JakubBohunicky/Oscilloscope/Sim/opamps.cir

[Main]
FileType=CIR
Version=12.00
Program=Micro-Cap
Component Version=10.00
Shape Version=11.00
Screen=2560,1440
MCAPVersion=12.2.0.5
Key ID=Demo
NLCnt=83
TXCnt=0

[shapedef]
Name=Battery
Line=0,0,22,0
Line=22,-3,22,3
Line=26,-7,26,7
Line=26,0,48,0
Current=32,8,16,8

[shapedef]
Name=Ground
Line=0,0,12,0
Line=12,-8,12,8
Line=18,-4,18,4
Line=24,0,24,0

[shapedef]
Name=Minus.root
Line=-2,0,2,0

[shapedef]
Name=Opamp7e
Root="Plus.root",14,6,0
Root="Minus.root",14,42,0
Line=0,0,8,0
Line=0,48,8,48
Line=8,-8,8,56
Line=8,56,72,24
Line=8,-8,72,24
Line=88,16,62,16
Line=56,32,88,32
Line=24,48,24,64
Line=24,0,24,-16
Root="Plus.root",18,-14,0
Root="Minus.root",18,62,0
Line=8,24,0,24
Ellipse=58,14,62,18
FColor=None

[shapedef]
Name=Plus.root
Line=-2,0,2,0
Line=0,-2,0,2

[shapedef]
Name=Resistor
PolyOpen=12
PolyLine=0,0
PolyLine=0,0
PolyLine=12,0
PolyLine=14,-4
PolyLine=18,4
PolyLine=22,-4
PolyLine=26,4
PolyLine=30,-4
PolyLine=34,4
PolyLine=36,0
PolyLine=48,0
PolyLine=48,0
Current=32,8,16,8

[shapedef]
Name=Sine_Source
Root="Vsource.root",0,0,0
Line=24,-6,26,-4
Line=26,-4,26,-2
Line=26,-2,22,2
Line=22,2,22,4
Line=22,4,24,6

[shapedef]
Name=Vsource.root
Line=0,0,12,0
Line=36,0,48,0
Ellipse=12,-12,36,12
FColor=None
Line=7,5,7,9
Root="Plus.root",41,7,0
Current=32,16,16,16

[compdef]
Name=Battery
Definition=Battery
Shape=Battery
Mask=6913
Used=55
memo=Battery
Label Offset=19,7,10,13
PinCnt=2
Pin="Plus",6,0,-4,-5
Pin="Minus",0,0,-10,-5

[compdef]
Name=Ground
Definition=Ground
Shape=Ground
Mask=1793
Used=308
memo=Ground
Label Offset=0,0,0,0
PinCnt=1
Pin="PinA",0,0,-3,-7

[compdef]
Name=Sine Source
Definition=Sine source
Shape=Sine_Source
Mask=4864
Used=1
memo=Sine Source
Label Offset=18,12,15,12
PinCnt=2
Pin="Plus",6,0,-6,-6
Pin="Minus",0,0,-19,-6

[compdef]
Name=Resistor
Definition=Resistor
Shape=Resistor
Mask=7937
Used=205
memo=Resistor
Label Offset=18,6,8,11
PinCnt=2
Pin="Plus",6,0,-10,-4
Pin="Minus",0,0,-14,-4

[compdef]
Name=AD8138_AD
Definition=Subckt
Shape=Opamp7e
Mask=4224
memo=Low Distortion Differential ADC Driver
Label Offset=46,40,-5,39
PinCnt=7
Pin="3A",a,0,0,-9,0
Pin="9",a,0,6,-3,0
Pin="99",a,3,-2,5,8
Pin="98",a,3,8,4,7
Pin="71",a,11,2,-5,0
Pin="71B",a,11,4,-5,0
Pin="110",a,0,3,-13,0

[compdef]
Name=ISL55211
Definition=Subckt
Shape=Opamp7e
Mask=4224
memo=Wideband, Low Noise, Low Distortion, Fixed Gain, Differential Amplifier BW=1.4GHz SR=5600V/us Av=2
Link=http://www.intersil.com/data/fn/fn7868.pdf
Label Offset=54,35,-4,43
PinCnt=7
Pin="IN-",a,0,6,-10,0
Pin="IN+",a,0,0,-10,0
Pin="V-",a,3,8,6,9
Pin="OUT-",a,11,2
Pin="OUT+",a,11,4
Pin="VCM",a,0,3,-18,0
Pin="V+",a,3,-2,5,6

[Circuit]
Window Placement=2,3, -1,-1, -8,-31, 0,0,1460,489
Default Object=Color=#000080
Default Object Font=Height=-15,FStyle=0,Color=#000080,Name=Arial
Default Object Apply Border To Text=No
Default Object Apply Fill To Text=No
Default Object GridSnap=No
NodeVoltageFormat=3
CurrentFormat=3
PowerFormat=3
PathDelayFormat=3
WarningFormat=3
GridTextFormulaFormat=3
Window Placement in Transient Probe=0,1, -1,-1, -8,-30, 633,0,1266,760
SpiceType=AMBIGUOUS
Title_Block_Border=None
Title_Block=False
Show Nodes=False
Show Voltages=True
Show Current=False
Show Power=False
Show Condition=False
Show Pin Connections=False
Show Connection Warnings=False
Show Cross=False
Show Attribute Text=True
Show Grid Text=True

[Comp]
Name=Battery
Px=168,312
Rot=3

[Attr]
ON=-26,-27,PART
V=V1
Style=8192

[Attr]
ON=-18,-41,VALUE
V=5
Style=8192

[Attr]
ON=0,0,PACKAGE
V

[Comp]
Name=Battery
Px=160,448
Rot=3

[Attr]
ON=-26,-27,PART
V=V2
Style=8192

[Attr]
ON=-18,-41,VALUE
V=5
Style=8192

[Attr]
ON=0,0,PACKAGE
V

[Wire]
Pxs=168,264,400,264

[Wire]
Pxs=400,264,400,304

[Wire]
Pxs=168,312,168,360

[Wire]
Pxs=160,400,168,400

[Comp]
Name=Ground
Px=168,360

[Wire]
Pxs=168,360,168,400

[Comp]
Name=Ground
Px=224,16
Rot=1

[Wire]
Pxs=160,448,400,448

[Wire]
Pxs=400,384,400,448

[Comp]
Name=Ground
Px=272,384
Rot=1

[Comp]
Name=Sine Source
Px=272,384
Rot=3

[Attr]
ON=-31,-26,PART
V=V3
Style=8192

[Attr]
ON=-39,-40,MODEL
V=fdfd

[Attr]
ON=0,0,PACKAGE
V

[Comp]
Name=Resistor
Px=320,328
Rot=4

[Attr]
ON=18,-20,PART
V=R1
Style=8192

[Attr]
ON=18,-34,RESISTANCE
V=500
Style=8192

[Attr]
ON=0,0,PACKAGE
V

[Comp]
Name=Resistor
Px=320,376
Rot=4

[Attr]
ON=-7,-18,PART
V=R2
Style=8192

[Attr]
ON=18,-33,RESISTANCE
V=523
Style=8192

[Attr]
ON=0,0,PACKAGE
V

[Wire]
Pxs=272,328,320,328

[Wire]
Pxs=272,328,272,336

[Comp]
Name=Ground
Px=320,376
Rot=1

[Comp]
Name=Resistor
Px=416,296
Rot=4

[Attr]
ON=18,-20,PART
V=R3
Style=8192

[Attr]
ON=18,-34,RESISTANCE
V=500
Style=8192

[Attr]
ON=0,0,PACKAGE
V

[Wire]
Pxs=368,296,368,320

[Wire]
Pxs=464,296,464,336

[Comp]
Name=Resistor
Px=424,424
Rot=4

[Attr]
ON=18,-20,PART
V=R4
Style=8192

[Attr]
ON=18,-34,RESISTANCE
V=500
Style=8192

[Attr]
ON=0,0,PACKAGE
V

[Wire]
Pxs=368,376,368,424

[Wire]
Pxs=368,424,424,424

[Wire]
Pxs=464,336,504,336

[Wire]
Pxs=472,352,472,424

[Wire]
Pxs=368,320,368,328

[Wire]
Pxs=368,320,376,320

[Wire]
Pxs=376,368,376,376

[Wire]
Pxs=368,376,376,376

[Wire]
Pxs=464,352,472,352

[Comp]
Name=AD8138_AD
Px=376,320

[Attr]
ON=46,40,PART
V=X1
Style=8192

[Attr]
ON=46,54,NAME
V=AD8138_AD

[Attr]
ON=46,82,PACKAGE
V=SO-8

[Wire]
Pxs=400,304,400,320

[Wire]
Pxs=368,296,416,296

[Wire]
Pxs=344,344,376,344

[Comp]
Name=ISL55211
Px=880,392

[Attr]
ON=54,35,PART
V=X3
Style=8192

[Attr]
ON=54,49,NAME
V=ISL55211

[Attr]
ON=0,0,PACKAGE
V

[Comp]
Name=Battery
Px=672,384
Rot=3

[Attr]
ON=-26,-27,PART
V=V103
Style=8192

[Attr]
ON=-18,-41,VALUE
V=3v3
Style=8192

[Attr]
ON=0,0,PACKAGE
V

[Wire]
Pxs=672,336,904,336

[Wire]
Pxs=904,336,904,376

[Wire]
Pxs=672,384,672,472

[Wire]
Pxs=664,472,672,472

[Wire]
Pxs=664,520,672,520

[Wire]
Pxs=904,456,904,520

[Comp]
Name=Resistor
Px=824,400
Rot=4

[Attr]
ON=18,-20,PART
V=R107
Style=8192

[Attr]
ON=18,-34,RESISTANCE
V=250
Style=8192

[Attr]
ON=0,0,PACKAGE
V

[Comp]
Name=Resistor
Px=824,448
Rot=4

[Attr]
ON=8,19,PART
V=R108
Style=8192

[Attr]
ON=10,4,RESISTANCE
V=250
Style=8192

[Attr]
ON=0,0,PACKAGE
V

[Wire]
Pxs=776,400,824,400

[Comp]
Name=Resistor
Px=920,368
Rot=4

[Attr]
ON=18,-20,PART
V=R109
Style=8192

[Attr]
ON=18,-34,RESISTANCE
V=500
Style=8192

[Attr]
ON=0,0,PACKAGE
V

[Wire]
Pxs=872,368,872,392

[Wire]
Pxs=968,368,968,408

[Comp]
Name=Resistor
Px=928,496
Rot=4

[Attr]
ON=18,-20,PART
V=R110
Style=8192

[Attr]
ON=18,-34,RESISTANCE
V=500
Style=8192

[Attr]
ON=0,0,PACKAGE
V

[Wire]
Pxs=872,448,872,496

[Wire]
Pxs=872,496,928,496

[Wire]
Pxs=968,408,1040,408

[Wire]
Pxs=976,456,976,496

[Wire]
Pxs=968,456,976,456

[Wire]
Pxs=872,392,872,400

[Wire]
Pxs=872,392,880,392

[Wire]
Pxs=880,440,880,448

[Wire]
Pxs=872,448,880,448

[Wire]
Pxs=968,424,976,424

[Wire]
Pxs=976,424,976,456

[Wire]
Pxs=872,368,920,368

[Wire]
Pxs=592,416,880,416

[Wire]
Pxs=904,376,904,392

[Wire]
Pxs=672,520,896,520

[Wire]
Pxs=672,472,672,520

[Comp]
Name=Ground
Px=896,520
Rot=1

[Wire]
Pxs=896,520,904,520

[Wire]
Pxs=504,304,504,336

[Wire]
Pxs=504,304,776,304

[Wire]
Pxs=776,304,776,400

[Wire]
Pxs=824,448,824,464

[Wire]
Pxs=504,464,824,464

[Wire]
Pxs=504,352,504,464

[Wire]
Pxs=472,352,504,352

[Comp]
Name=Resistor
Px=1040,456
Rot=5

[Attr]
ON=8,-25,PART
V=R111
Style=8192

[Attr]
ON=8,-39,RESISTANCE
V=100
Style=8192

[Attr]
ON=0,0,PACKAGE
V

[Wire]
Pxs=976,496,1040,496

[Wire]
Pxs=1040,456,1040,496

[Wire]
Pxs=592,416,592,560

[Wire]
Pxs=336,560,592,560

[Wire]
Pxs=336,528,336,560

[Wire]
Pxs=344,344,344,528

[Wire]
Pxs=336,528,344,528

[Schematic]
CurrentSection 0=0
CurrentSection 1=0
CurrentSection 2=0
CurrentSection 3=0
Splitter.xs=0
Splitter.ys=0
TextQuad=4099
Scale=0.66666666666666663
GridUser=10
ShapeGroups="Main","Euro","Polarity","Main1","Main11","Electrolytic","GroundArrow","DeMorgan"
CalcRMS=False
CalcAVG=False
CalcPeak=False
CalcVoltage=True
DisplayMeasure=Last
ShareScales=True

[Tools]
Pos=Top
FILESAVEASOLD=No
BOM=No
FILEPCB=No
PROBE=Yes
SELECT=Yes
PAN=Yes
COMP=Yes
TEXT=Yes
WIRE=Yes
WIRED=Yes
BUS=Yes
GRAPHIC=Yes
FLOWCHART=Yes
LINE=No
ELLIPSE=No
RECT=No
DIAM=No
ARC=No
PIE=No
TRIANGLE=No
STAR=No
LEFTBRK=No
RIGHTBRK=No
BOTHBRK=No
META=No
PARALLELOGRAM=No
FC_PROCESS=No
FC_ALT_PROCESS=No
FC_DECISION=No
FC_DATA=No
FC_PREDEFPROCESS=No
FC_INTERNALSTORAGE=No
FC_DOCUMENT=No
FC_MULTIDOCUMENT=No
FC_TERMINATOR=No
FC_PREPARATION=No
FC_MANUALINPUT=No
FC_MANUALOPERATION=No
FC_CONNECTOR=No
FC_OFFPAGECONNECTOR=No
FC_PUNCHCARD=No
FC_PUNCHEDTAPE=No
FC_SUMMING_JUNCTION=No
FC_OR=No
FC_COLLATE=No
FC_SORT=No
FC_EXTRACT=No
FC_MERGE=No
FC_STORED_DATA=No
FC_DELAY=No
FC_SAS=No
FC_MAGNETIC_DISK=No
FC_DAS=No
FC_DISPLAY=No
SPREAD_SHEET=Yes
POLYCLOS=No
POLYOPEN=No
FLAG=Yes
INFO=Yes
HELP=Yes
HELP_SPICE=No
LINK=Yes
CHECK=Yes
REGION_ENABLE=Yes
TITLE_BLOCK=Yes
DIGTRC=No
DIGTRC2=No
BUILD_COMMAND=Yes
DIGALL=No
GRIDTEXT=Yes
COMPTEXT=Yes
NODE=Yes
MEASURED=Yes
NODEV=Yes
CURRENT=Yes
POWER=Yes
CONDITIN=Yes
PIN=Yes
CONNWARN=Yes
CROSS=No
GRID=Yes
BORDER=Yes
BORDERONE=Yes
TITLE=Yes
RUBBER=Yes
PROPERTY=Yes
STEP=Yes
MIRROR=Yes
ROTATE=Yes
FLIPY=Yes
FLIPX=Yes
CIR_MAKEMACRO=No
CLEARCUTWIRE=No
CLIPBOARDCIRPAGE2BMM=No
FINDCOMP=Yes
FIND=Yes
REPEAT=No
REPLACE=No
MODEL=Yes
CIR2CKT=No
ATTDISP=No
ENABLE=Yes
DISABLE=Yes
ENABLE_WITH=Yes
TOFRONT=Yes
TOBACK=Yes
SELNEXT=No
PAGEADD=No
PAGEADDTEXT=No
ADDSECTION=No
PAGEDEL=No
ZOOMIN=Yes
ZOOMOUT=Yes
AUTOSCALECIR=Yes
GOTOFLAG=No
UPLEVEL=Yes
COLOR=Yes
FONT=Yes
STYLE=Yes
DM_LAST=No
DM_RMS=No
DM_AVG=No
DM_PEAK=No
GRID_NONE=No
GRID_NORMAL=No
GRID_BOLD_5=No
GRID_BOLD_6=No
GRID_BOLD_USER=No
GRAPH_PAPER=No
SPLITCIRTEXTH=No
SPLITCIRTEXTV=No
SPACE_SPLITTERS_EVENLY=No
NORMALCIR=No
RENAMEDEFINE=No
RENAMECMP=No
ATTALIGN=No
RESETNODEPOS=No
FIT2STANDARD=No
NODESNAP=No
MOVETEXT=No
TEXTINC=No
TOGGLETEXT=No
TOGGLEMODE=No
TOLERANCE=No
ALIGNAB=No
ALIGNLEFT=No
ALIGNCENTER=No
ALIGNRIGHT=No
ALIGNTOP=No
ALIGNMIDDLES=No
ALIGNBOTTOM=No

[Section]
Index=0
Name="opamp"
Type=Main
Enable=True
CurrentPage 0=0
CurrentPage 1=0
CurrentPage 2=0
CurrentPage 3=0
TabSize 0=425
TabSize 1=425
TabSize 2=425
TabSize 3=425

[Page]
Index=0
Section=0
Print=True
Enable=True
Name=Main
PrinterScale=1
Scale 0=1
Scale 1=1
Scale 2=1
Scale 3=0.66666666666666663
Px=345,541
WinBackGround Color=#FFFFFF
Select Color=#FF0000
Anchor Color=#000000
Select Box Color=#000080
Grid Text Color=Height=-12,FStyle=0,Color=#0000FF,Name=Verdana
Grid Text RTF=False
Grid Text Angle=0
Grid Text GridSnap=True
Grid Text PinIt=False
Grid Text JustifyH=Left
Grid Text JustifyV=Bottom
Grid GradientColor2=None
Grid OutlineThickness=1
Grid OutlineColor=None
Component Color=#0000FF
Attribute Text=Height=-12,FStyle=0,Color=#008000,Name=Verdana
Wire Color=#008000
Bus Color=#008000
Pin Connection=Height=-10,FStyle=0,Color=#FF0000,Name=Arial
Pin Marker Color=#008000
Node Number=Height=-11,FStyle=0,Color=#FF00FF,Name=Arial
Node Voltage Color=Height=-11,FStyle=0,Color=#000000,Name=Arial
Dynamic AC Voltage Color=#E4E4E4
Text Banner Text=Height=-15,FStyle=0,Color=#800000,Name=Arial
Title Block Background=#C0C0C0
Current=Height=-11,FStyle=0,Color=#0000FF,Name=Arial
Power/Condition=Height=-11,FStyle=0,Color=#FF0000,Name=Arial
Digital Path Color=#FF0000
Title Block Border=#000000
Disabled	Color=#C0C0C0
Search Color=#FFFF00
Grid Color=#000000
Graph Paper=#E4E4E4
Digital 0 Color=#000000
Digital R Color=#FFFF00
Digital F Color=#FFFF00
Digital 1 Color=#FF0000
Digital X Color=#C0C0C0
Digital Z Color=#808080
Block Select Color=#51F998

[Page]
Index=1
Section=0
Type=Text
Print=False
Enable=True
Name=Text
SB 0=0,2
Font=Height=-15,FStyle=0,Color=#000000,Name=Courier New
Comment Color=#008000
WinBackGround Color=#FFFFFF
Disabled	Color=#C0C0C0
KeyWord Color=#0000FF
Error	Color=#FF0000
Search Color=#FFFF00

[Page]
Index=2
Section=0
Type=Text
Print=False
Enable=True
Name=Models
SB 0=22,17
Font=Height=-15,FStyle=0,Color=#000000,Name=Courier New
Comment Color=#008000
WinBackGround Color=#FFFFFF
Disabled	Color=#C0C0C0
KeyWord Color=#0000FF
Error	Color=#FF0000
Search Color=#FFFF00

[Page]
Index=3
Section=0
Type=Info
Print=False
Enable=True
Name=Info
Font=Height=-15,FStyle=0,Color=#000000,Name=Courier New
Comment Color=#008000
WinBackGround Color=#FFFFFF
Disabled	Color=#C0C0C0
KeyWord Color=#0000FF
Error	Color=#FF0000
Search Color=#FFFF00

[Text Area]
Section=0
Page=1
Text=.OPTIONS ITL4=50
Text=.OPTIONS ITL1=250
Text=.OPTIONS PIVREL=1

[Text Area]
Section=0
Page=2
Text=* Schematic File
Text=*
Text=* Syntax:
Text=* .MODEL <model name> [AKO:<reference model name>] <ModelType>
Text=* +([<parameter name>=<value>][LOT[/#][/GAUSS|/UNIFORM|/WCASE]=[<tol>[%]] |[-<low>%,<high>%]][DEV[/#][/GAUSS|/UNIFORM|/WCASE]=[<tol>[%]]...)
Text=* ModelType must be one of OPA,D,NPN,NMOS,NJF,PUL,SIN,TRN,CORE,GASFET,VSWITCH,ISWITCH,CAP,IND,RES,PNP,PMOS,PJF,DOUTPUT,DINPUT,UADC,UDAC,UGATE,UTGATE,UEFF,UGFF,UDLY,UPLD,UROM,URAM,UBGT,UIO,LPNP,NIGBT,I,V
Text=*
Text=*Examples:
Text=* .MODEL 2N2222A NPN(BF=150 IS=1E-14)
Text=* .model M1 NMOS(KP=2.5E-5 VTO=1.345 CGDO=14.67p CGBO=4.566p)
Text=* .MODEL DK D(IS=1E-18)
Text=* .model 2N2222A AKO:2N2222 NPN (BF=55 ISE=10F)
Text=* .Model BJT1 NPN (RE=12 LOT/1/GAUSS=30% DEV/2/UNIFORM=2%)
Text=*
Text=* A .cir file is typically found in the data directory
Text=*
Text=
Text=.MODEL FDFD SIN (F=1k)

[InfoPage]
InfoPage=True
Warnings=True
System=True
Defines=True
Array=True
Model=True
Measure=True
MacroSubckt=True
NotUsed=True
ComponentCounts=True
VariablizePaths=False
DontShowPaths=False
SimulationLog=True

[Transient]
WinID=1
Font=Height=-19,FStyle=0,Color=#0000FF,Name=Arial
WinBackGround Color=#FFFFFF
Select Color=#FF0000
Anchor Color=#000000
Select Box Color=#000080
Window Placement in Probe=0,1, -1,-1, 0,0, 0,0,633,760
Title
AutoTitle=Yes
Grid Color=#808080
Grid Weight=1
Grid Pattern=Dot6
Tracker Foreground=Height=-15,FStyle=0,Color=#000000,Name=Arial
Tracker Background=#FFFF00
Baseline color=#0000FF
BaseLine Weight=1
CurveFit color=#FF0000
CurveFit Weight=2
CurveFit Pattern=Dash
Static Grids=False
PlusMark=False
MinorLog25=Off
LabelMinor=Off
DataPoints=False
Token=False
Ruler=False
XAxisGrids=True
YAxisGrids=True
MinorLogGrids=True
BaseLine=False
AlignZ=True
Align Cursors=True
TagFormatX=3
TagFormatY=3
FormulaFormat=2
EndMode=SCALE
Graph Background=#FFFFFF
Tracker Intercept=False
Tracker Mouse=True
Tracker Cursor=True
Tracker Cursor BranchInfo=False
Horizontal Cursor=False
Same Y Scales=Yes
Enable X Scaling=True
Enable Y Scaling=True
Keep X Scales The Same=True
Number of Grids X=5
Number of Grids Y=5
Cursor Select Color Primary=#C0C0C0
Cursor Select Color Secondary=#FF0000
Data Point Labels Color Fore=Height=-15,FStyle=0,Color=#000000,Name=Arial
Data Point Labels Color Back=#FFFF00
OperPoint=True
OperPointOnly=False
AutoScaleRanges=True
FixedTimeStep=False
DoPSS=False
PSS_Periods="1"
PSS_Iterations="5"
PSS_Error="1u"
PSS_ShowPlots=True
FFT_NPts="8192"
FFT_IncludeDCHarmonic=False
FFT_AutoScale_Harmonics="10"
PrinterAutoTile=No
PrinterBlackBorder=No
AnimateWait=None
AnimateWaitTime=500
AnimatePressAfter=0
Save_For_Future=No
Reduce_Display=1
Reduce_Save=1
Reduce_ThrowDataOut=0
Num Out Header Left
Num Out Header Center="$MC\n$user\n$company\n$Analysis of $name\n$date $time"
Num Out Header Right
Num Out Delimiter=32
Num Out Write=True
Num Out Write Main Header=True
Num Out Write Limits=True
Num Out Write Branch Header=True
Num Out Write Models=False
Num Out Write Zero Models=True
Num Out Write Undefined Models=True
Num Out Write Operating Point=True
Num Out Write Measurement Values=True
Num Out Write Tolerance Detail=True
Num Out Write Values=True
Num Out Write Waveform Header=True
Num Out Allow Dup Y Expr=False
Num Out Low="TSTART"
Num Out High="TMAX"
Num Out Font=Height=-15,FStyle=0,Color=#000000,Name=Courier New
Num Out Format=3
Num Out HideNonSelected=False
Num Out UseActualDataPoints=False
AutoSaveWave=False
Wave Format=16E
State Variables Format=5E
Print Individual Pages=False

[Tools]
Pos=Top
SELECT=Yes
PAN=Yes
GRAPHIC=Yes
LINE=No
ELLIPSE=No
RECT=No
DIAM=No
ARC=No
PIE=No
TRIANGLE=No
STAR=No
LEFTBRK=No
RIGHTBRK=No
BOTHBRK=No
META=No
PARALLELOGRAM=No
POLYCLOS=No
POLYOPEN=No
SCALE=Yes
CURSOR=Yes
MEASUREH=Yes
MEASUREV=Yes
TAG=Yes
PTAG=Yes
TEXT=Yes
PROPERTY=Yes
START=Yes
STOP=Yes
PAUSE=Yes
RESUME=No
DATAPTS=Yes
TOKENS=Yes
RULER=Yes
PLUS=Yes
XAXIS=Yes
YAXIS=Yes
MINORLOG=Yes
LOG25=Yes
BASELINE=Yes
HORIZCUR=Yes
GOTOX=Yes
GOTOY=Yes
GOTOPERF=Yes
GOTOBRNC=Yes
CLEAR_ACCUMULATED=Yes
PDELETE_ALL_PLOTS=Yes
NEXT=Yes
NEXTIN=Yes
PEAK=Yes
VALLEY=Yes
HIGH=Yes
LOW=Yes
INFLECTN=Yes
GHIGH=Yes
GLOW=Yes
BOTTOM=Yes
TOP=Yes
WAVEFORMBUFFER=Yes
AOUTPUT=Yes
PKEY=Yes
ENXSCALE=Yes
ENYSCALE=Yes
ZOOMIN=Yes
ZOOMOUT=Yes
AUTOSCALE=Yes
RESTORESCALE=No
COLOR=Yes
FONT=Yes
STYLE=Yes
SELNEXT=No
NORMALIZE=No
NORMALIZE_MIN=No
NORMALIZE_MAX=No
ADD_TAG_LEFT=No
ADD_TAG_RIGHT=No
ADD_HORZ_TAG=No
ADD_VERT_TAG=No
ALIGN_CURSORS=No
ALIGN_CURSORSZ=No
CURSORTOCLIPBOARD=No
TRACKER_CURSOR=No
TRACKER_CURSOR_BRANCHINFO=No
TRACKER_INTERCEPT=No
TRACKER_MOUSE=No
TOFRONT=Yes
TOBACK=Yes
SPLITCIRTEXTH=No
SPLITCIRTEXTV=No
SPACE_SPLITTERS_EVENLY=No
NORMALCIR=No
LABEL_WAVEFORM=No
LABEL_DATA_POINTS=No
WFB_ADD_TO_LIMITS=No
ENVELOPE=No
SAMEYSCALES=No
KEEPXSCALESTHESAME=No
CURVEFIT=No
ADD_MARKER=No
SHOWWATCH=No
BP=No
TOGGLEMODE=No
REMOVEALLTEXT=No
AUTOSCALEX=No
LABELALLMINOR=No
ALIGNLEFT=No
ALIGNCENTER=No
ALIGNRIGHT=No
ALIGNTOP=No
ALIGNMIDDLES=No
ALIGNBOTTOM=No

[APage]
Analysis=Transient
Name="Main"

[Monte Carlo Options]
Analysis=Transient
Status=Off
Zero Tolerance=False
Eliminate Outliers=False
Distribution=Normal
Number of Runs=10
Seed=0

[Limits]
Analysis=Transient
TMax=2m
TStart=0
TStep=2u
NPts=51
Temp=27
RetraceRuns=1
StateVar=Zero
RunOption=Normal
Temperature Type=Linear
Accumulate Plots=False
IgnoreExprErrors=False

[WaveForm]
Analysis=Transient
Plt=1
AliasID=1
XExp=T
YExp=v(1)
XRng=Auto
YRng=Auto
Options=LINEARX,LINEARY
Enable=Enable
Line Color=#0000FF
Text Color=#0000FF
Rainbow=False
VFmtX=3
VFmtY=3
ScaleFactorX="None"
ScaleFactorY="None"
ScaleUnitsX="Auto"
ScaleUnitsY="Auto"
SFmtX=2
SFmtY=2
NOFmtX=3E
NOFmtY=3E

[WaveForm]
Analysis=Transient
Plt=1
AliasID=2
XExp=T
YExp=v(2)
XRng=Auto
YRng=Auto
Options=LINEARX,LINEARY
Enable=Enable
Line Color=#FF0000
Text Color=#FF0000
Rainbow=False
VFmtX=3
VFmtY=3
ScaleFactorX="None"
ScaleFactorY="None"
ScaleUnitsX="Auto"
ScaleUnitsY="Auto"
SFmtX=2
SFmtY=2
NOFmtX=3E
NOFmtY=3E

[WaveForm]
Analysis=Transient
AliasID=-1
Options=LINEARX,LINEARY
Enable=Enable
Line Color=#008000
Text Color=#008000
Rainbow=False
VFmtX=3
VFmtY=3
ScaleFactorX="None"
ScaleFactorY="None"
ScaleUnitsX="Auto"
ScaleUnitsY="Auto"
SFmtX=2
SFmtY=2
NOFmtX=3E
NOFmtY=3E

[Limits]
Analysis=DynamicAC
FirstValueDisplay=Mag
SecondValueDisplay=PhaseDeg
PlaceText=True

[Limits]
Analysis=DynamicDC
Temp=27
SliderPer=10
PlaceText=True

[Pane]
Analysis=Transient

[Pane]
Analysis=AC

[Pane]
Analysis=DC

[Pane]
Analysis=HmDistortion

[Pane]
Analysis=ImDistortion

[Pane]
Analysis=Stability

[Watch]
Analysis=Transient
Format=3
ExprPercentWidth=80

[WCTolerance]
Var Width=100
Nominal Width=72
Tol Width=152
Tol Name=Drift
Col Width Neq=50
Col Width Pos=50
Col Width Rnd=50

[WCFiles]
UseFile=<Library>Standard.tlib
AVAILABLE_FILE=<Library>Standard.tlib

[OPMethods]
Analysis=Transient
Standard Newton-Raphson=0,0
Source Stepping=0,0
Diagonal Gmin Stepping=0,0
Junction Gmin Stepping=0,0
Pseudo Transient=0,0

[OPMethods]
Analysis=AC
Standard Newton-Raphson=0,0
Source Stepping=0,0
Diagonal Gmin Stepping=0,0
Junction Gmin Stepping=0,0
Pseudo Transient=0,0

[OPMethods]
Analysis=DC
Standard Newton-Raphson=0,0
Source Stepping=0,0
Diagonal Gmin Stepping=0,0
Junction Gmin Stepping=0,0
Pseudo Transient=0,0

[OPMethods]
Analysis=HmDistortion
Standard Newton-Raphson=0,0
Source Stepping=0,0
Diagonal Gmin Stepping=0,0
Junction Gmin Stepping=0,0
Pseudo Transient=0,0

[OPMethods]
Analysis=ImDistortion
Standard Newton-Raphson=0,0
Source Stepping=0,0
Diagonal Gmin Stepping=0,0
Junction Gmin Stepping=0,0
Pseudo Transient=0,0

[OPMethods]
Analysis=Stability
Standard Newton-Raphson=0,0
Source Stepping=0,0
Diagonal Gmin Stepping=0,0
Junction Gmin Stepping=0,0
Pseudo Transient=0,0

[OPMethods]
Analysis=DynamicAC
Standard Newton-Raphson=0,0
Source Stepping=0,0
Diagonal Gmin Stepping=0,0
Junction Gmin Stepping=0,0
Pseudo Transient=0,0

[OPMethods]
Analysis=DynamicDC
Standard Newton-Raphson=0,0
Source Stepping=0,0
Diagonal Gmin Stepping=0,0
Junction Gmin Stepping=0,0
Pseudo Transient=0,0
